offgridsystems/Documents/DK battery cell holder - OSHW/20160526_102511.jpg

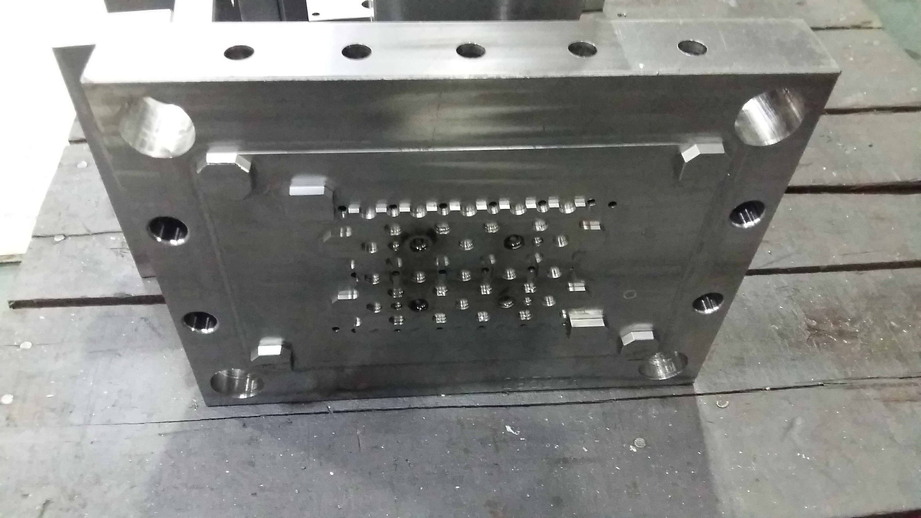
DK battery cell holder - OSHW/20160526_102511.jpg
